Luucas237/Master-Thesis/polsl-aei-theses-main/single-file/Obrazy/Nastawy/wykres_A_Modelnercyjny.png

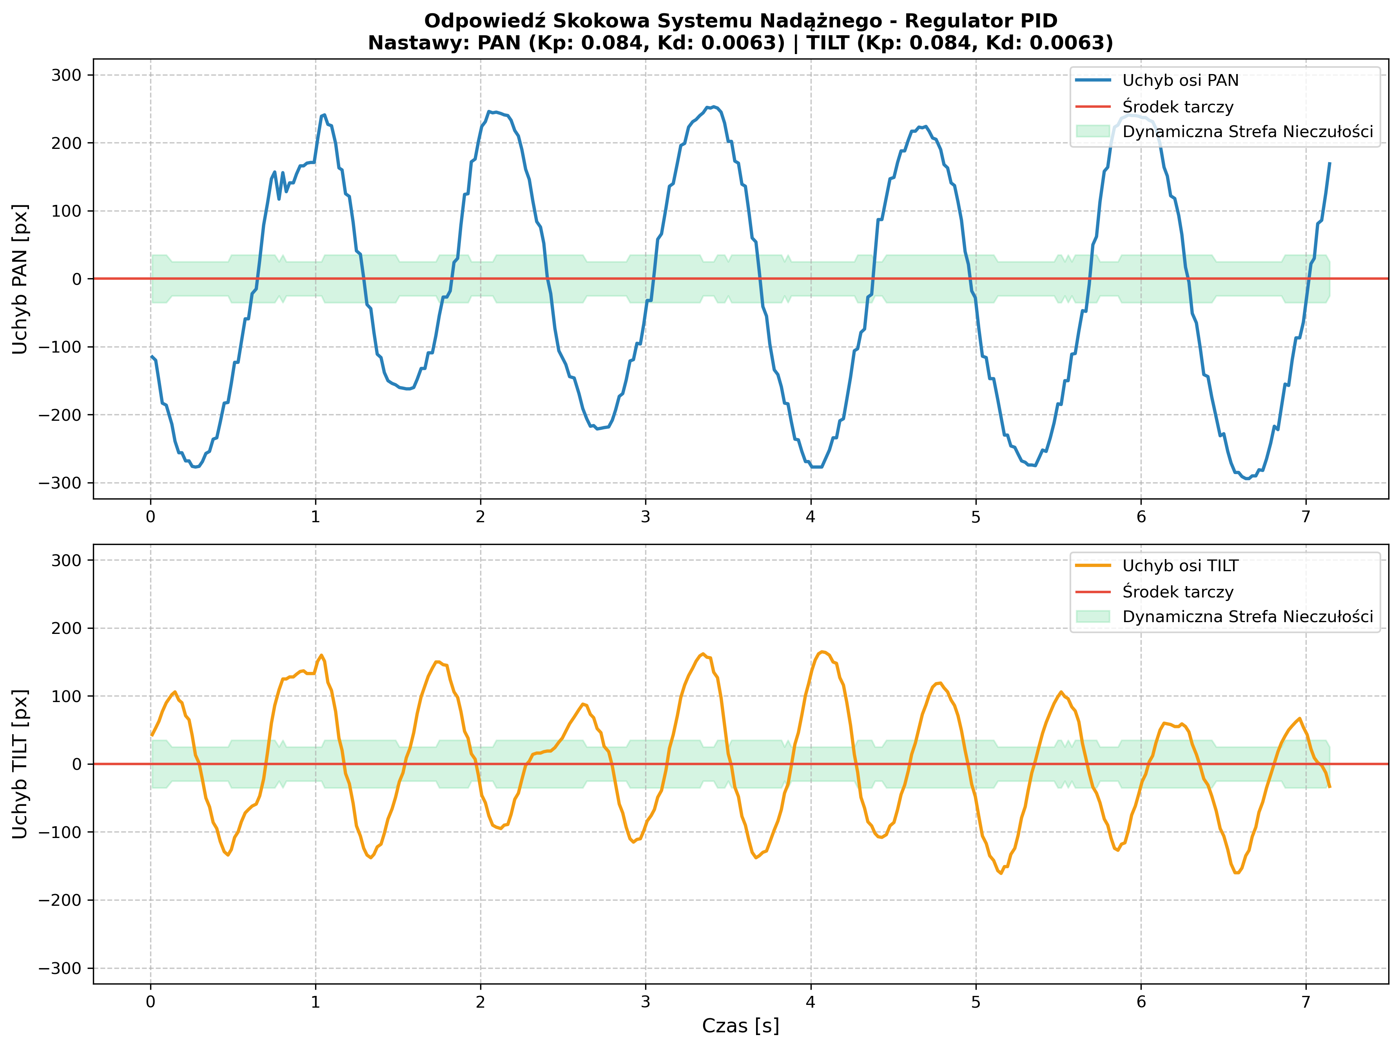
Color_detection_ros_Ubuntu/src/pan_tilt_description/data/Figures/wykres_A_Modelnercyjny.png
