Luucas237/Master-Thesis/Color_detection_ros_Ubuntu/src/pan_tilt_description/data/Figures/wykres_PID_up.png

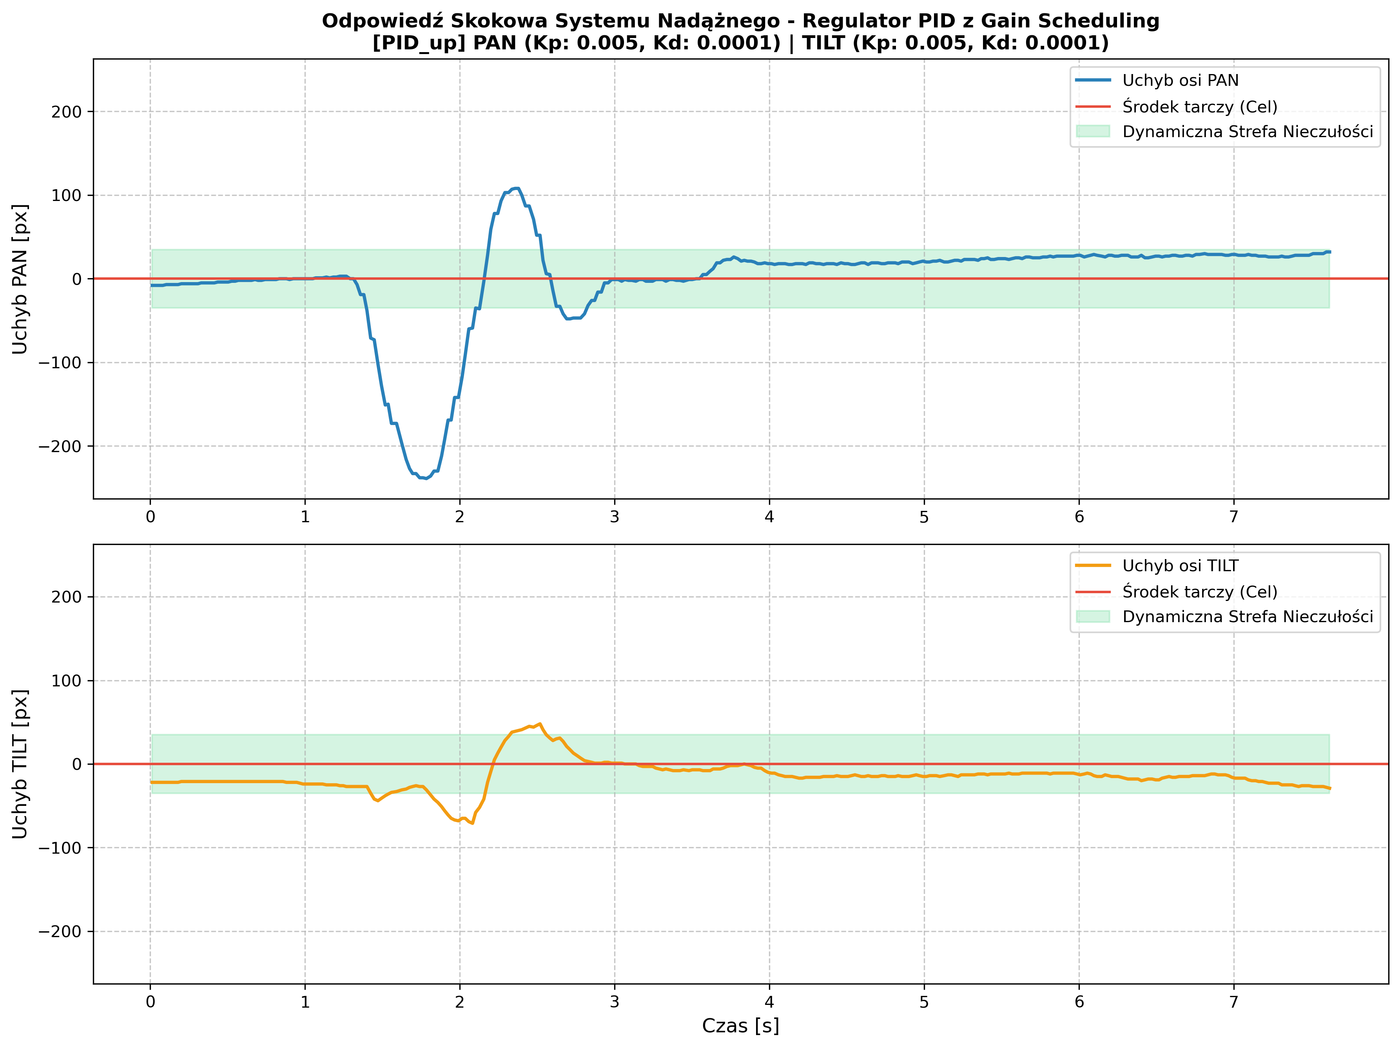
Color_detection_ros_Ubuntu/src/pan_tilt_description/data/Figures/wykres_PID_up.png
