Luucas237/Master-Thesis/Model/Magisterka/18650-cell-holder-1.snapshot.1/18650 Cell Holder 2.jpg

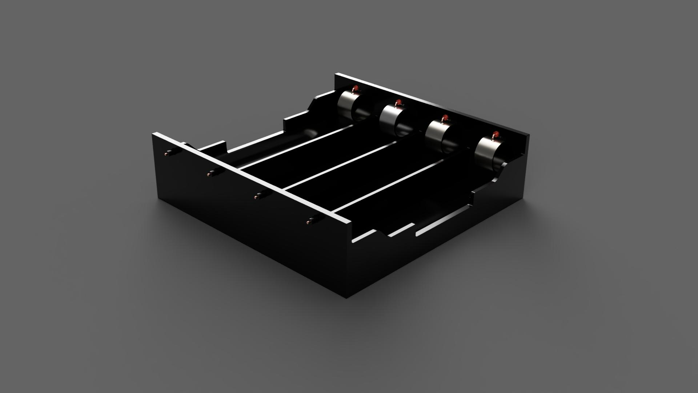
Model/Magisterka/18650-cell-holder-1.snapshot.1/18650 Cell Holder 2.jpg
