Luucas237/Master-Thesis/Model/Magisterka/aixiz-12mm-laser-diode-module-5-6mm-1.snapshot.1/Aixiz/Exploded Module.png

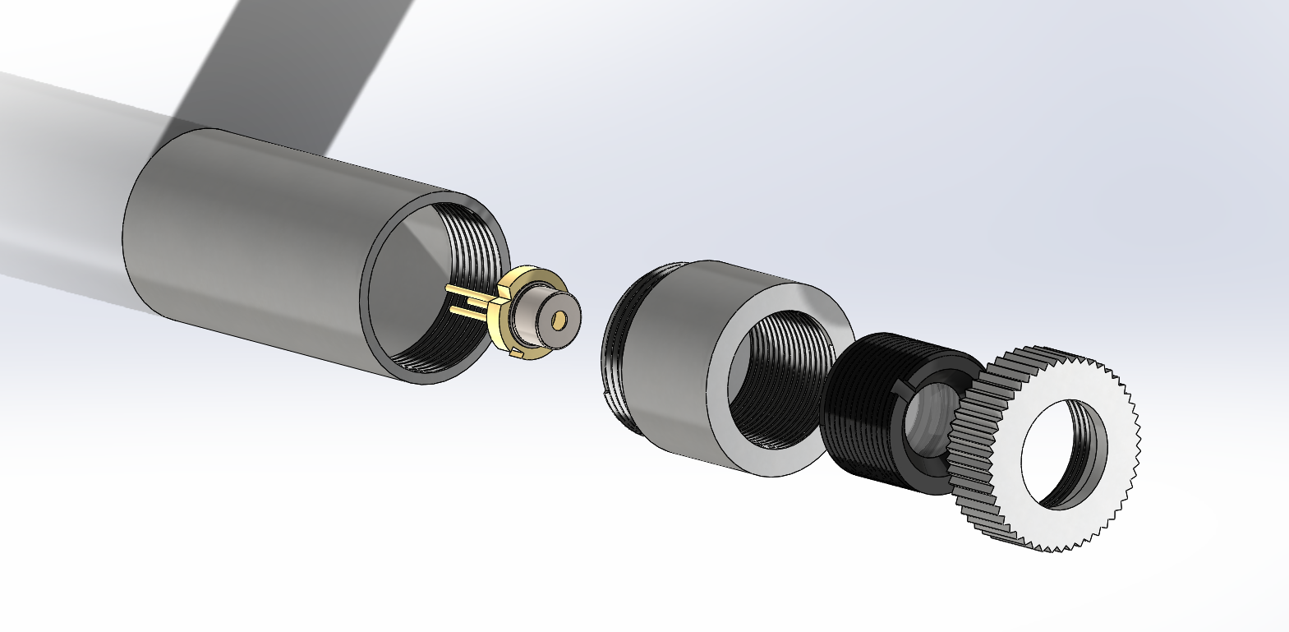
Model/Magisterka/aixiz-12mm-laser-diode-module-5-6mm-1.snapshot.1/Aixiz/Exploded Module.png
