Luucas237/Master-Thesis/polsl-aei-theses-main/single-file/Obrazy/20025458.jpg

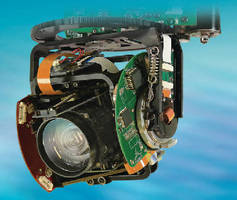
polsl-aei-theses-main/single-file/Obrazy/20025458.jpg
