Luucas237/Master-Thesis/polsl-aei-theses-main/single-file/Obrazy/applsci-10-01923-g001.png

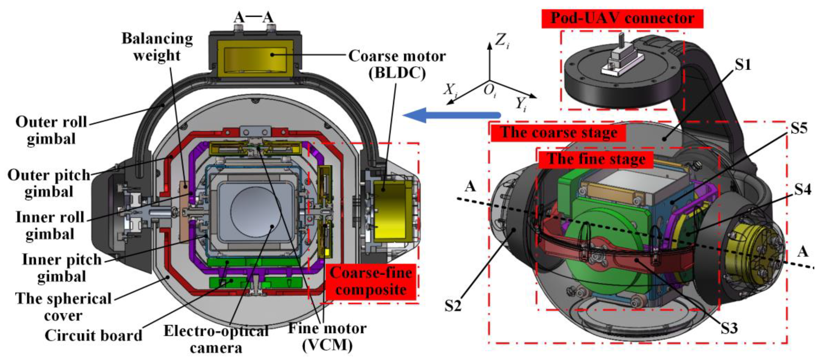
polsl-aei-theses-main/single-file/Obrazy/applsci-10-01923-g001.png
