Luucas237/Master-Thesis/polsl-aei-theses-main/single-file/Obrazy/Gazebo/Good_1.png

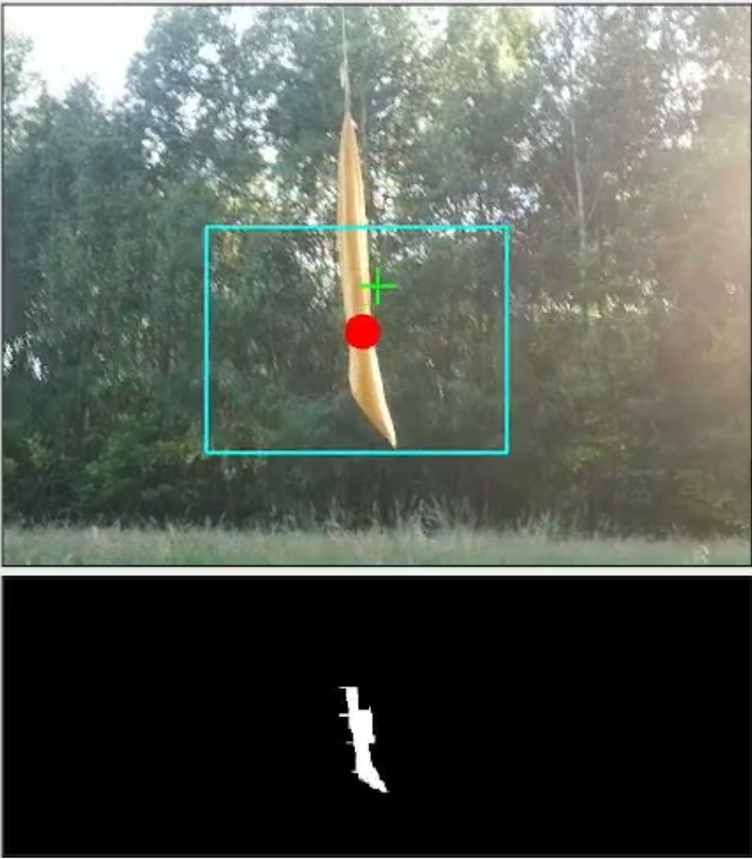
polsl-aei-theses-main/single-file/Obrazy/Gazebo/Good_1.png
