Luucas237/Master-Thesis/polsl-aei-theses-main/single-file/Obrazy/images.jpg

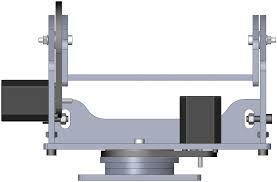
polsl-aei-theses-main/single-file/Obrazy/images.jpg
