Luucas237/Master-Thesis/polsl-aei-theses-main/single-file/Obrazy/Inventor/podstawa dol.png

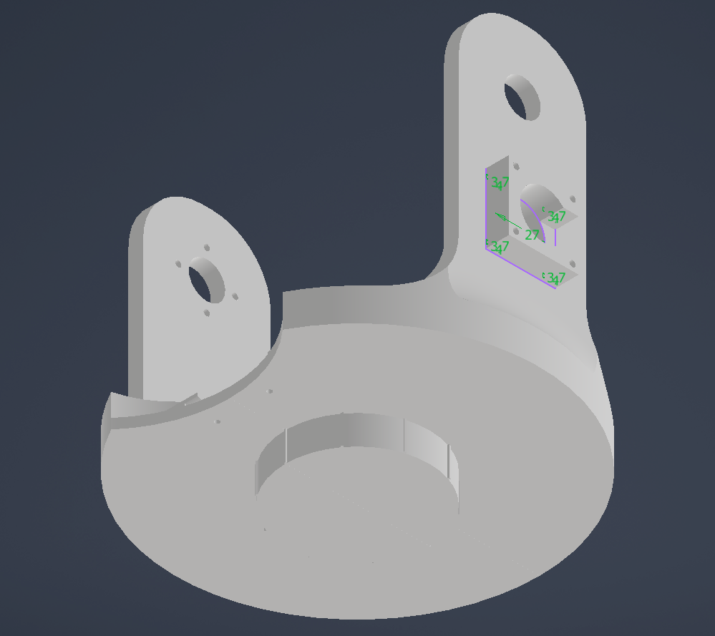
polsl-aei-theses-main/single-file/Obrazy/Inventor/podstawa dol.png
