Luucas237/Master-Thesis/polsl-aei-theses-main/single-file/Obrazy/Nastawy/wykres_bang_LP.png

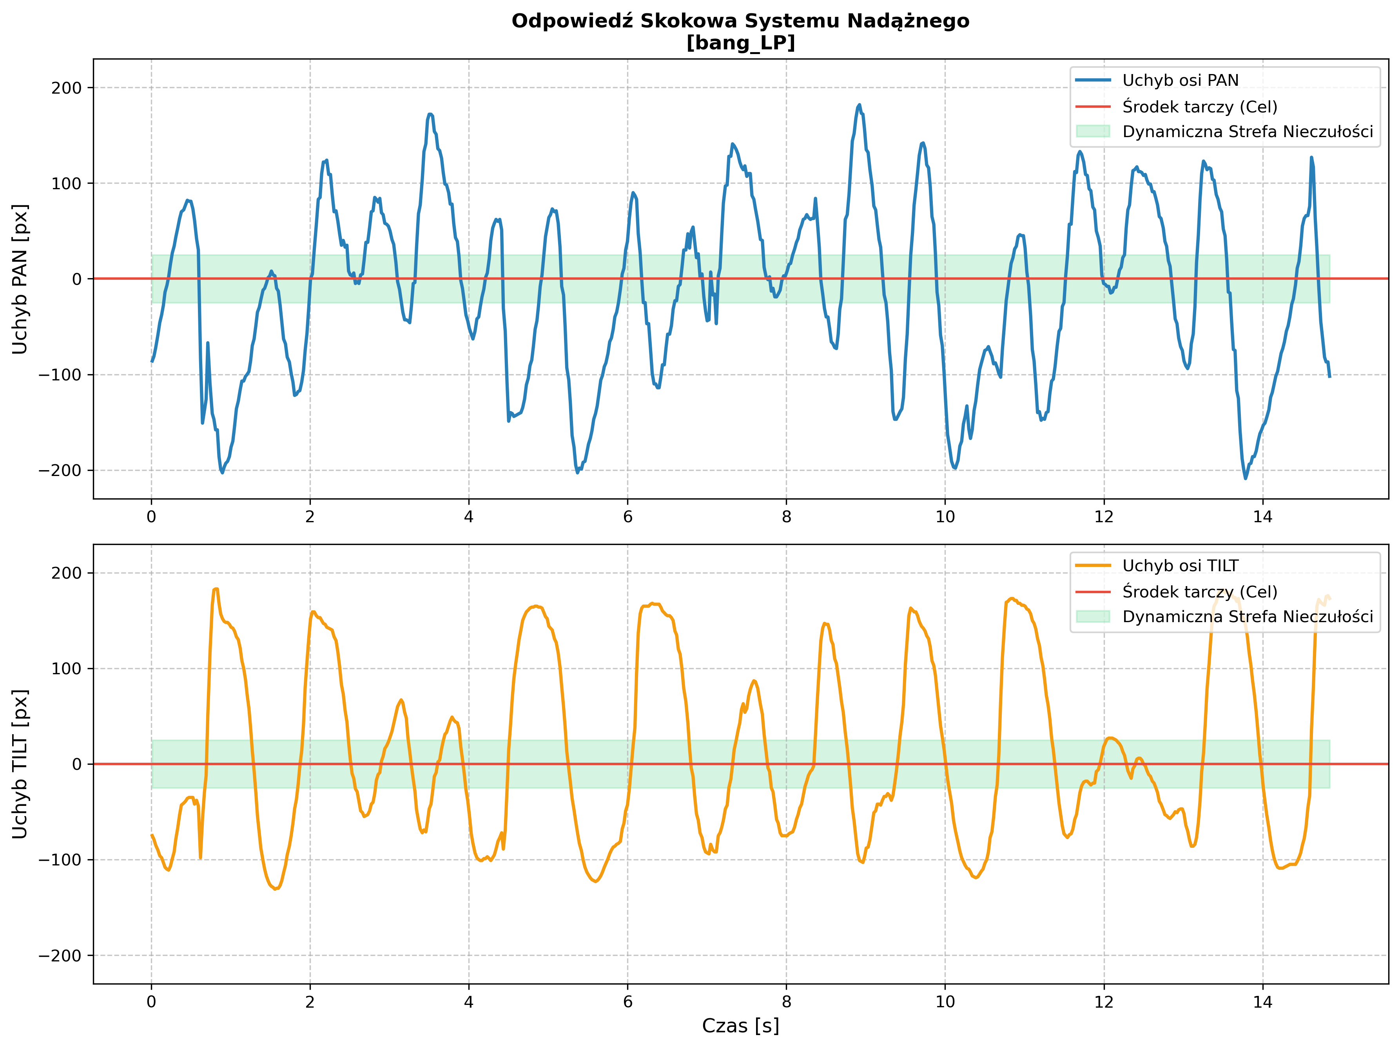
polsl-aei-theses-main/single-file/Obrazy/Nastawy/wykres_bang_LP.png
