Luucas237/Master-Thesis/polsl-aei-theses-main/single-file/Obrazy/NPT-4M-36X-75TIZ-HD-LRF3-GS (CYB2304) Front-2K.png

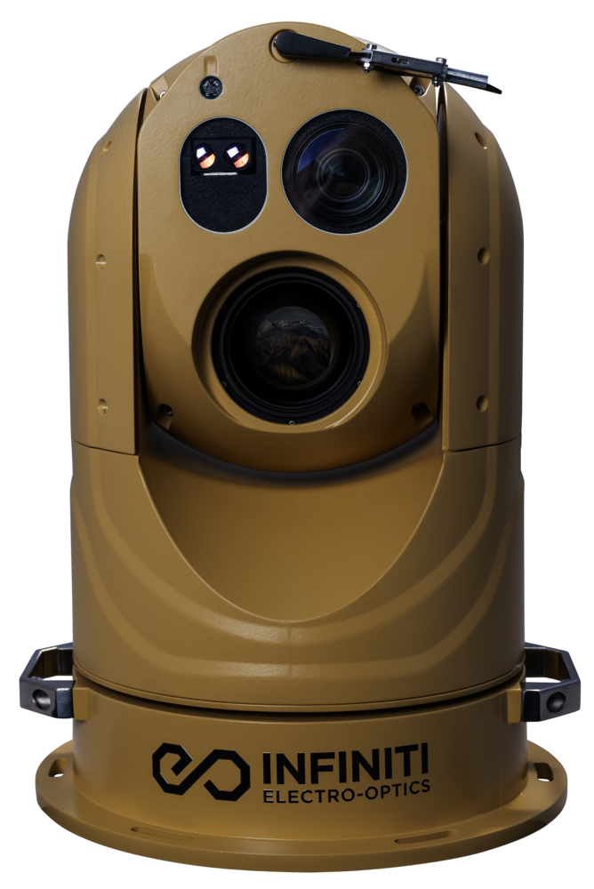
polsl-aei-theses-main/single-file/Obrazy/NPT-4M-36X-75TIZ-HD-LRF3-GS (CYB2304) Front-2K.png
