Luucas237/Master-Thesis/polsl-aei-theses-main/single-file/Obrazy/Real/pomiary_2.jpeg

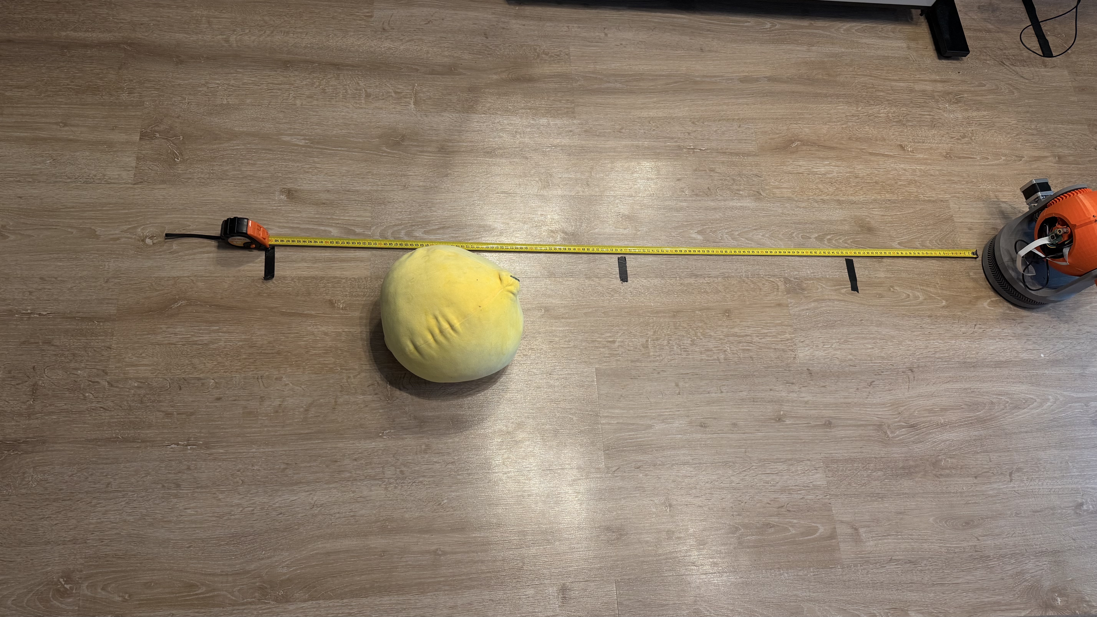
polsl-aei-theses-main/single-file/Obrazy/Real/pomiary_2.jpeg
