Luucas237/Master-Thesis/polsl-aei-theses-main/single-file/Obrazy/Real/pomiary_3.jpeg

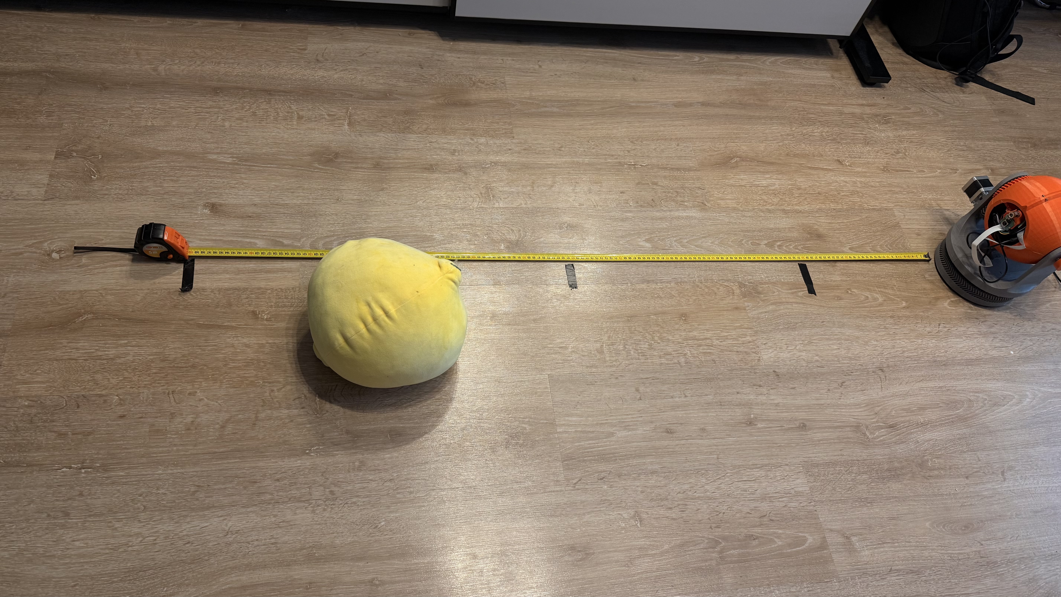
polsl-aei-theses-main/single-file/Obrazy/Real/pomiary_3.jpeg
