Luucas237/Master-Thesis/polsl-aei-theses-main/single-file/Obrazy/Schemat elektryczny/Caly.png

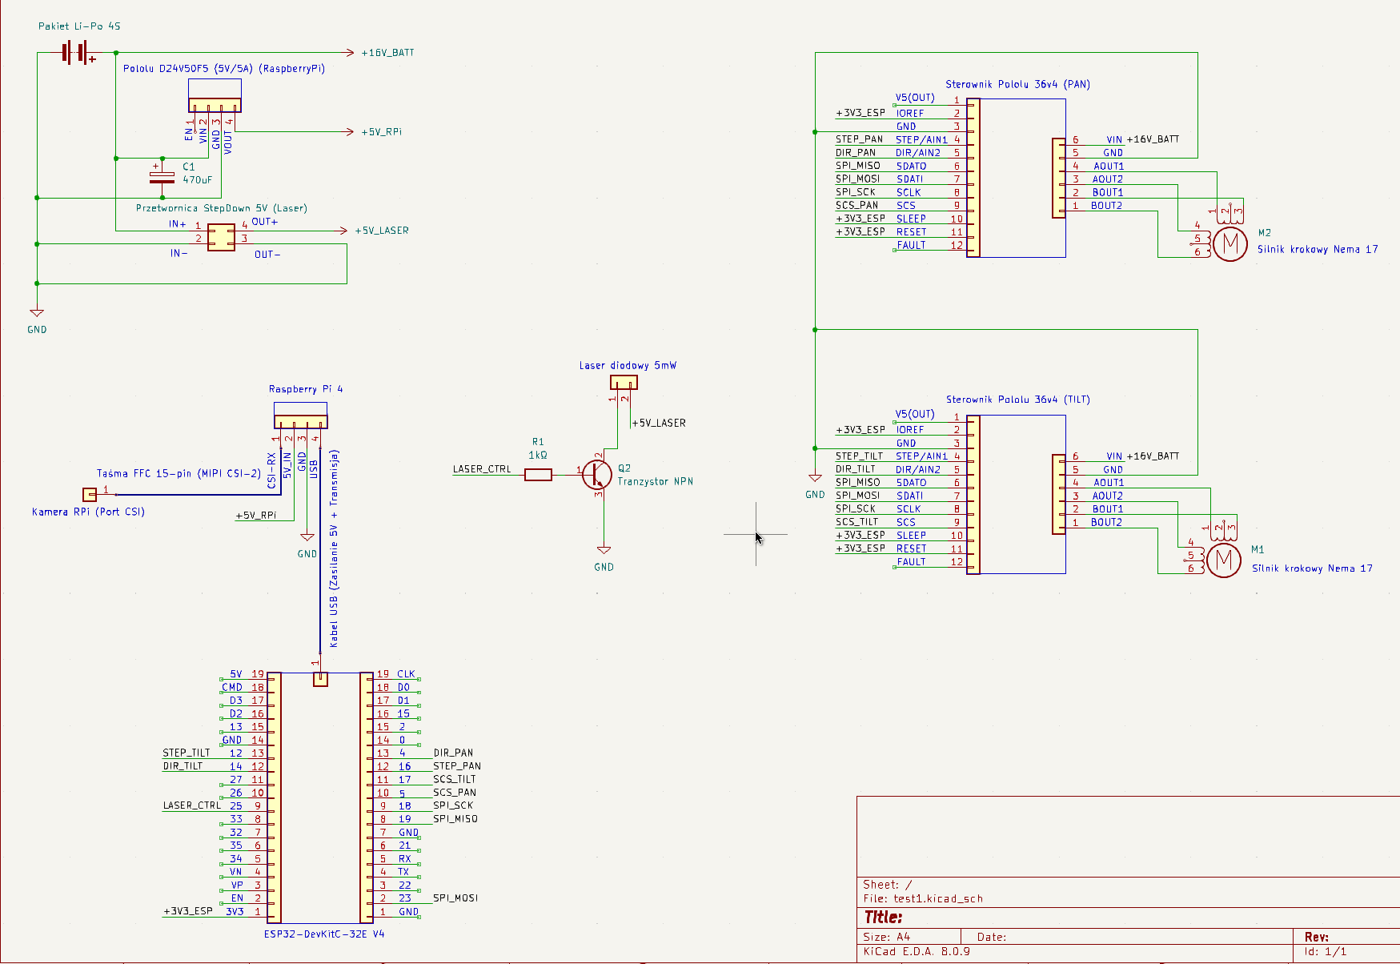
polsl-aei-theses-main/single-file/Obrazy/Schemat elektryczny/Caly.png
