Luucas237/Master-Thesis/polsl-aei-theses-main/single-file/Obrazy/Securitex_Cut_Away_Homburg.jpg

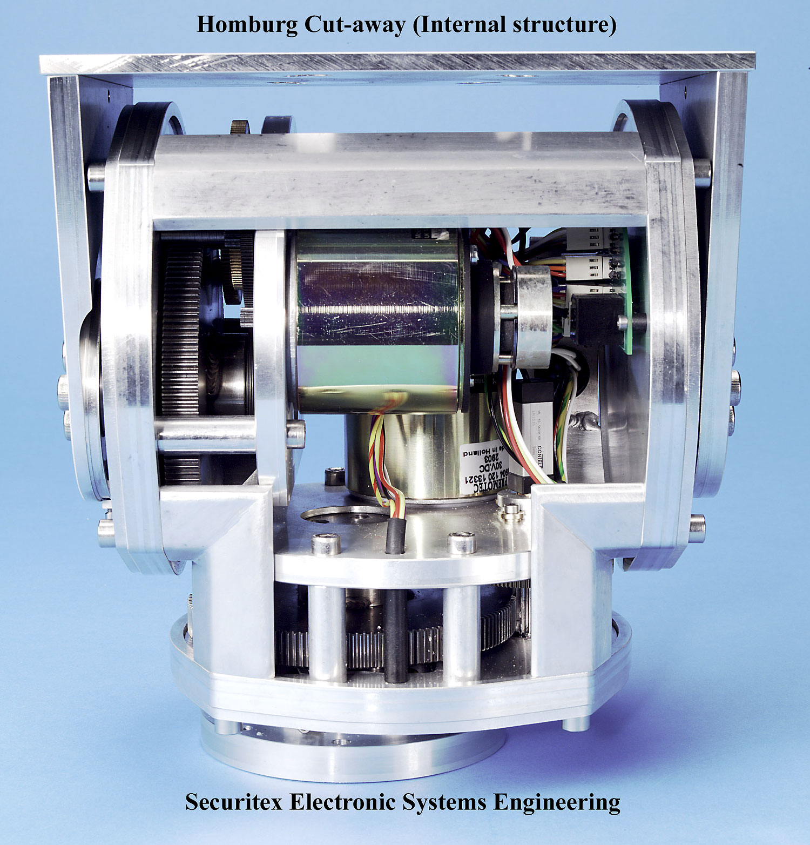
polsl-aei-theses-main/single-file/Obrazy/Securitex_Cut_Away_Homburg.jpg
