Luucas237/Master-Thesis/Model/Magisterka/aixiz-12mm-laser-diode-module-5-6mm-1.snapshot.1/Aixiz/Acrylic Lens.SLDPRT

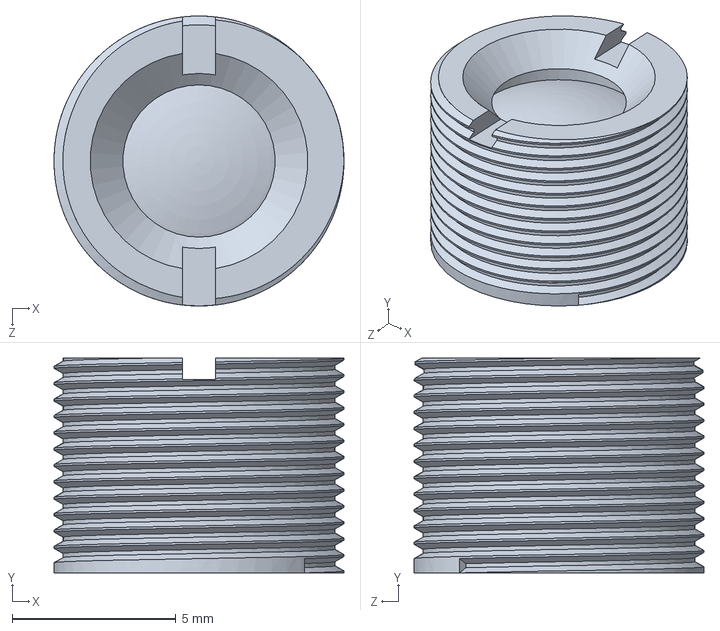
[picture p101: CAD file, 2026-03-24]
Model/Magisterka/aixiz-12mm-laser-diode-module-5-6mm-1.snapshot.1/Aixiz/Acrylic Lens.SLDPRT
8.86 x 6.56 x 8.86 mm
