Luucas237/Master-Thesis/Model/Magisterka/esp32-devkitc-v4-1.snapshot.1/ESP-WROOM-32D-Export/ab2_usb_micro_smd.wrl.SLDPRT

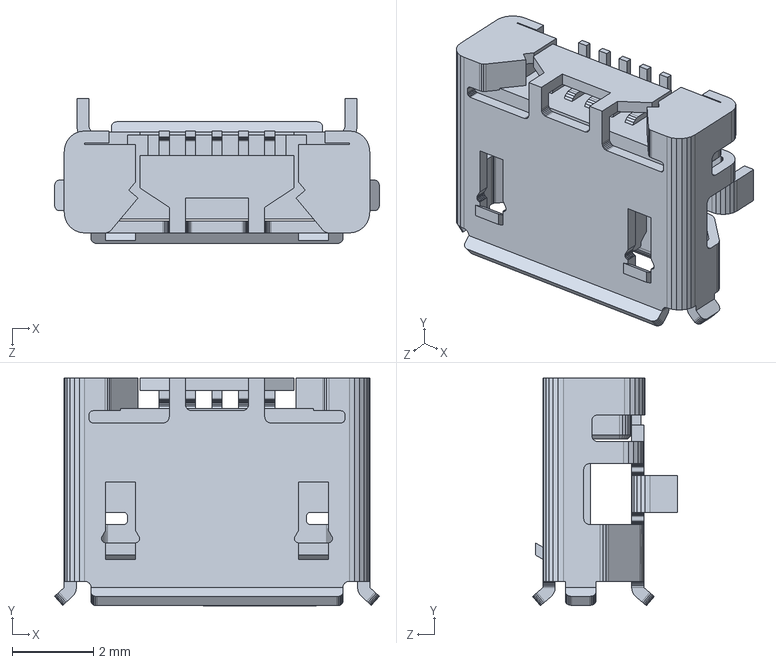
[picture p102: CAD file, 2026-03-24]
Model/Magisterka/esp32-devkitc-v4-1.snapshot.1/ESP-WROOM-32D-Export/ab2_usb_micro_smd.wrl.SLDPRT
8.00 x 5.60 x 3.57 mm
