Luucas237/Master-Thesis/Model/Magisterka/esp32-devkitc-v4-1.snapshot.1/ESP-WROOM-32D-Export/ESP32-chip.SLDPRT

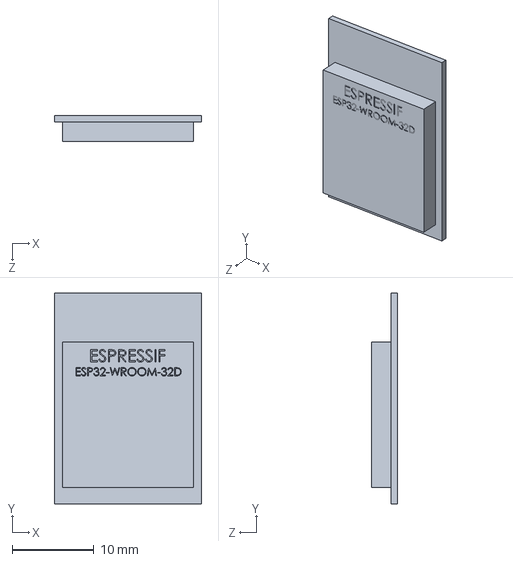
[picture p103: CAD file, 2026-03-24]
Model/Magisterka/esp32-devkitc-v4-1.snapshot.1/ESP-WROOM-32D-Export/ESP32-chip.SLDPRT
18.0 x 25.8 x 3.20 mm
