Luucas237/Master-Thesis/Model/Magisterka/18650-cell-holder-1.snapshot.1/18650 Cell Holder.step

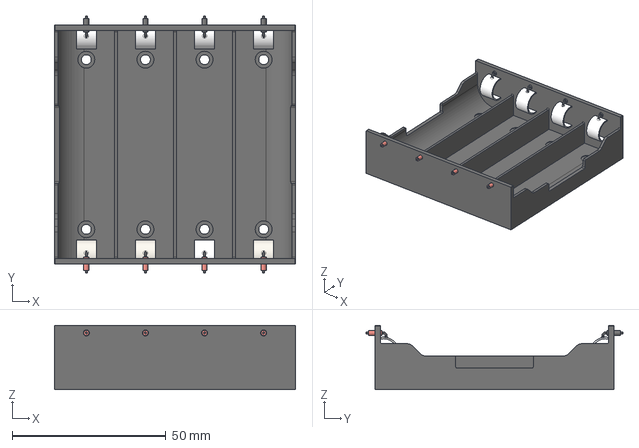
[picture p104: CAD file, 2026-03-24]
Model/Magisterka/18650-cell-holder-1.snapshot.1/18650 Cell Holder.step
78.6 x 83.7 x 21.0 mm
